butzist/phoniesp32/web/src/main.rs

#![feature(try_blocks)]
use dioxus::prelude::*;
use dioxus_bulma as b;
pub(crate) mod components;
pub(crate) mod layouts;
pub(crate) mod metadata;
pub(crate) mod pages;
pub(crate) mod services;

use components::ToastManager;
use layouts::Layout;
use pages::{Associations, Files, NewAssociation, Playback, Settings, UploadPage};

#[derive(Debug, Clone, Routable, PartialEq)]
#[rustfmt::skip]
enum Route {
    #[layout(Layout)]
    #[route("/")]
    Playback {},

    #[route("/associations")]
    Associations {},

    #[route("/files")]
    Files {},

    #[route("/upload")]
    UploadPage {},

    #[route("/new-association")]
    NewAssociation {},

    #[route("/settings")]
    Settings {},
}

const FAVICON: Asset = asset!("/assets/favicon.ico");
const STYLES: Asset = asset!("/assets/styles.scss");

fn main() {
    dioxus::launch(App);
}

#[component]
fn App() -> Element {
    use_context_provider(ToastManager::new);

    rsx! {
        document::Link { rel: "icon", href: FAVICON }
        document::Stylesheet { href: STYLES }
        b::BulmaProvider { theme: b::BulmaTheme::Auto, load_bulma_css: false,
            Router::<Route> {}
            components::ToastContainer {}
        }
    }
}
