butzist/phoniesp32/firmware/src/drivers/rfid.rs

use alloc::format;
use alloc::rc::Rc;
use defmt::{debug, error, info};
use embassy_executor::Spawner;
use embassy_sync::blocking_mutex::raw::CriticalSectionRawMutex;
use embassy_sync::blocking_mutex::raw::NoopRawMutex;
use embassy_sync::channel::Channel;
use embassy_sync::mutex::Mutex;
use embassy_sync::signal::Signal;
use embassy_time::{Duration, Timer};
use esp_hal::gpio::{AnyPin, Input, InputConfig, Level, Output, OutputConfig, Pull};
use esp_hal::time::Rate;
use heapless::String;
use mfrc522_async::{EnableError, Mfrc522};
use unwrap_infallible::UnwrapInfallible;

use crate::drivers::spi_bus;

use {esp_backtrace as _, esp_println as _};

use spi_bus::SpiDevice;

type MyMfrc522 = Mfrc522<SpiDevice, Input<'static>, Output<'static>, mfrc522_async::Unknown>;

pub enum RfidScanResult {
    Found(String<8>),
    NotFound,
    Error,
}

pub struct RfidHandleInner {
    scan_trigger: Signal<CriticalSectionRawMutex, ()>,
    scan_result: Channel<NoopRawMutex, RfidScanResult, 1>,
    last_fob: Mutex<CriticalSectionRawMutex, Option<String<8>>>,
}

impl RfidHandleInner {
    pub fn trigger_scan(&self) {
        self.scan_trigger.signal(());
    }

    pub async fn wait_for_scan_result(&self) -> RfidScanResult {
        self.scan_result.receive().await
    }

    pub async fn get_last_fob(&self) -> Option<String<8>> {
        self.last_fob.lock().await.clone()
    }
}

pub type RfidHandle = Rc<RfidHandleInner>;

pub struct Rfid {
    rfid: MyMfrc522,
    handle: RfidHandle,
}

impl Rfid {
    pub async fn new(
        shared_spi: spi_bus::SharedSpi,
        cs: AnyPin<'static>,
        irq: AnyPin<'static>,
        rfid_enable: AnyPin<'static>,
    ) -> Self {
        let rfid = Self::create_device(shared_spi, cs, irq, rfid_enable);
        let handle = Rc::new(RfidHandleInner {
            scan_trigger: Signal::new(),
            scan_result: Channel::new(),
            last_fob: Mutex::new(None),
        });
        Self { rfid, handle }
    }

    fn create_device(
        shared_spi: spi_bus::SharedSpi,
        cs: AnyPin<'static>,
        irq: AnyPin<'static>,
        rfid_enable: AnyPin<'static>,
    ) -> Mfrc522<SpiDevice, Input<'static>, Output<'static>, mfrc522_async::Unknown> {
        let spi_dev = spi_bus::make_spi_device(shared_spi, cs, Rate::from_mhz(10));
        let irq = Input::new(irq, InputConfig::default().with_pull(Pull::Up));
        let enable = Output::new(rfid_enable, Level::Low, OutputConfig::default());
        Mfrc522::new(spi_dev, irq, enable)
    }

    pub fn spawn(self, spawner: &Spawner) -> RfidHandle {
        let handle = self.handle;
        spawner.must_spawn(rfid_task(self.rfid, handle.clone()));
        handle
    }
}

#[embassy_executor::task]
async fn rfid_task(mut rfid: MyMfrc522, handle: RfidHandle) {
    loop {
        handle.scan_trigger.wait().await;
        handle.scan_trigger.reset();
        debug!("RFID: scan triggered");

        let rfid_device = rfid
            .enable()
            .map_err(EnableError::into_error)
            .unwrap_infallible();

        let result = match rfid_device.init().await {
            Ok(mut rfid_device) => match rfid_device.reqa().await {
                Ok(atqa) => {
                    Timer::after(Duration::from_millis(50)).await;
                    if let Ok(uid) = rfid_device.select(&atqa).await {
                        let uid_bytes = uid.as_bytes();

                        let hex_str = format!(
                            "{:02x}{:02x}{:02x}{:02x}",
                            uid_bytes[0], uid_bytes[1], uid_bytes[2], uid_bytes[3]
                        );

                        let fob_str = String::try_from(hex_str.as_str()).unwrap();
                        handle.last_fob.lock().await.replace(fob_str.clone());
                        info!("RFID: FOB scanned: {}", fob_str);

                        rfid = rfid_device
                            .disable()
                            .map_err(EnableError::into_error)
                            .unwrap_infallible()
                            .into_unknown();

                        RfidScanResult::Found(fob_str)
                    } else {
                        rfid = rfid_device
                            .disable()
                            .map_err(EnableError::into_error)
                            .unwrap_infallible()
                            .into_unknown();

                        RfidScanResult::NotFound
                    }
                }
                Err(err) => {
                    if err != mfrc522_async::Error::Timeout {
                        error!("RFID: error: {:?}", defmt::Debug2Format(&err));
                    }

                    rfid = rfid_device
                        .disable()
                        .map_err(EnableError::into_error)
                        .unwrap_infallible()
                        .into_unknown();

                    RfidScanResult::NotFound
                }
            },
            Err(e) => {
                error!(
                    "RFID: initialization failed: {:?}",
                    defmt::Debug2Format(e.error())
                );

                let uninitialized_device = e.into_device();
                rfid = uninitialized_device
                    .disable()
                    .map_err(EnableError::into_error)
                    .unwrap_infallible()
                    .into_unknown();

                RfidScanResult::Error
            }
        };

        handle.scan_result.send(result).await;
    }
}
