butzist/phoniesp32/firmware/src/lib.rs

#![no_std]
#![recursion_limit = "256"]
#![feature(impl_trait_in_assoc_type)]
#![feature(stmt_expr_attributes)]
#![feature(trivial_bounds)]

use core::future::Future;

use alloc::string::String;
use defmt::{error, warn};
use serde::{Deserialize, Serialize};

extern crate alloc;

#[derive(Serialize, Deserialize, Clone)]
pub struct DeviceConfig {
    #[serde(alias = "SSID")]
    pub ssid: String,

    #[serde(alias = "PASSWORD")]
    pub password: String,
}

// When you are okay with using a nightly compiler it's better to use https://docs.rs/static_cell/2.1.0/static_cell/macro.make_static.html
#[macro_export]
macro_rules! mk_static {
    ($t:ty,$val:expr) => {{
        static STATIC_CELL: static_cell::StaticCell<$t> = static_cell::StaticCell::new();
        #[deny(unused_attributes)]
        let x = STATIC_CELL.uninit().write($val);
        x
    }};
}

impl defmt::Format for DeviceConfig {
    fn format(&self, fmt: defmt::Formatter) {
        defmt::write!(
            fmt,
            "DeviceConfig {{ SSID: {}, PASSWORD: {} }}",
            self.ssid.as_str(),
            self.password.as_str(),
        )
    }
}

pub async fn retry<F, R, E>(mut f: F, times: u8) -> Result<R, E>
where
    F: AsyncFnMut() -> Result<R, E>,
{
    for _ in 0..times - 1 {
        if let Ok(val) = f().await {
            return Ok(val);
        }
    }

    f().await
}

pub trait PrintErr<T> {
    fn print_warn(self, message: &str) -> Option<T>;
    fn print_err(self, message: &str) -> Option<T>;
}

impl<T, E> PrintErr<T> for Result<T, E>
where
    E: defmt::Format,
{
    fn print_warn(self, message: &str) -> Option<T> {
        match self {
            Ok(val) => Some(val),
            Err(err) => {
                warn!("{}: {}", message, err);
                None
            }
        }
    }

    fn print_err(self, message: &str) -> Option<T> {
        match self {
            Ok(val) => Some(val),
            Err(err) => {
                error!("{}: {}", message, err);
                None
            }
        }
    }
}

/// Extends a mutable reference's lifetime to `'static`.
///
/// # Safety
///
/// The caller must guarantee:
/// - The referenced data will remain valid for the entire program lifetime
///   (i.e. it is never deallocated, and no `core::mem::forget` is called
///    on the owner that would skip destructors).
/// - There are no concurrent mutable aliases to the same data
///   (no data races).
/// - The reference points to valid, properly aligned memory.
///
/// Typical legitimate uses on embedded MCUs:
/// - Memory-mapped peripheral registers at fixed addresses.
/// - DMA buffers allocated via `dma_buffers!()` into static memory.
pub unsafe fn extend_to_static<T>(r: &mut T) -> &'static mut T {
    let ptr = r as *mut T;
    unsafe { &mut *ptr }
}

/// Allows to await an Option<Future>
pub async fn opt_async<F, R>(f: Option<F>) -> Option<R>
where
    F: Future<Output = R>,
{
    Some(f?.await)
}

pub fn with_extension(
    basename: &str,
    ext: &str,
) -> Result<heapless::String<12>, heapless::CapacityError> {
    let mut fname = heapless::String::<12>::new();
    fname.push_str(basename)?;
    fname.push_str(ext)?;
    Ok(fname)
}

pub mod controllers;
pub mod drivers;
pub mod entities;
pub mod peripherals;
pub mod services;
