butzist/phoniesp32/firmware/src/mdns.rs

use core::net::Ipv4Addr;
use edge_mdns::buf::{BufferAccess, VecBufAccess};
use edge_mdns::domain::base::Ttl;
use edge_mdns::io::{self, DEFAULT_SOCKET, MdnsIoError};
use edge_mdns::{HostAnswersMdnsHandler, host::Host};
use edge_nal::UdpSplit;
use edge_nal_embassy::{Udp, UdpBuffers};
use embassy_executor::Spawner;
use embassy_net::Stack;
use embassy_sync::blocking_mutex::raw::NoopRawMutex;
use embassy_sync::signal::Signal;
use embassy_time::{Duration, Timer};
use esp_println::println;

const SERVICE_NAME: &str = "phoniesp32";

pub struct MdnsResponder {
    stack: Stack<'static>,
}

impl MdnsResponder {
    pub fn new(stack: Stack<'static>) -> Self {
        Self { stack }
    }

    pub fn spawn(self, spawner: &Spawner) {
        spawner.must_spawn(mdns_responder(self.stack));
    }
}

#[embassy_executor::task]
async fn mdns_responder(stack: Stack<'static>) {
    println!("Starting mDNS responder for {}", SERVICE_NAME);

    let (recv_buf, send_buf) = mk_static!(
        (
            VecBufAccess<NoopRawMutex, 1500>,
            VecBufAccess<NoopRawMutex, 1500>
        ),
        (VecBufAccess::new(), VecBufAccess::new(),)
    );

    let udp_buffers = mk_static!(UdpBuffers<1>, UdpBuffers::new());

    let signal = Signal::new();

    loop {
        let ipv4 = wait_for_network_ready(&stack).await;
        let udp = Udp::new(stack, udp_buffers);
        match run_mdns(udp, recv_buf, send_buf, &signal, ipv4).await {
            Ok(_) => {
                println!("mDNS responder completed successfully");
                Timer::after(Duration::from_secs(1)).await;
            }
            Err(e) => {
                println!("mDNS responder error: {:?}", e);
                Timer::after(Duration::from_secs(5)).await;
            }
        }
    }
}

async fn wait_for_network_ready(stack: &Stack<'_>) -> Ipv4Addr {
    loop {
        if stack.is_link_up()
            && let Some(config) = stack.config_v4()
        {
            let ip = config.address.address();
            if !ip.is_unspecified() {
                println!("Network ready, IP: {}", ip);
                return ip;
            }
        }
        Timer::after(Duration::from_millis(500)).await;
    }
}

struct SimpleRng {
    seed: u32,
}

impl SimpleRng {
    fn new() -> Self {
        Self { seed: 12345 }
    }
}

impl rand_core::RngCore for SimpleRng {
    fn next_u32(&mut self) -> u32 {
        self.seed = self.seed.wrapping_mul(1103515245).wrapping_add(12345);
        self.seed
    }

    fn next_u64(&mut self) -> u64 {
        let hi = self.next_u32() as u64;
        let lo = self.next_u32() as u64;
        (hi << 32) | lo
    }

    fn fill_bytes(&mut self, dest: &mut [u8]) {
        for chunk in dest.chunks_mut(4) {
            let bytes = self.next_u32().to_le_bytes();
            chunk.copy_from_slice(&bytes[..chunk.len()]);
        }
    }
}

async fn run_mdns<RB, SB>(
    udp: Udp<'_>,
    recv_buf: &RB,
    send_buf: &SB,
    signal: &Signal<NoopRawMutex, ()>,
    ipv4: Ipv4Addr,
) -> Result<(), MdnsIoError<edge_nal_embassy::UdpError>>
where
    RB: BufferAccess<[u8]>,
    SB: BufferAccess<[u8]>,
{
    let mut socket = io::bind(&udp, DEFAULT_SOCKET, Some(Ipv4Addr::UNSPECIFIED), Some(0)).await?;

    let (recv, send) = socket.split();

    let host = Host {
        hostname: SERVICE_NAME,
        ipv4,
        ipv6: core::net::Ipv6Addr::UNSPECIFIED,
        ttl: Ttl::from_secs(60),
    };

    let rng = SimpleRng::new();

    let mdns = io::Mdns::<_, _, _, _, _, NoopRawMutex>::new(
        Some(Ipv4Addr::UNSPECIFIED),
        Some(0),
        recv,
        send,
        recv_buf,
        send_buf,
        rng,
        signal,
    );

    mdns.run(HostAnswersMdnsHandler::new(&host)).await
}
